bml3mk5/USBKeyboard4S1/Software/USBKeyboard4S1.X/interrupt.h

/** @file   interrupt.h
 *
 *  @author Sasaji
 *  @date   2018/02/10
 *
 * 	@brief  interrupt 
 */

#ifndef INTERRUPT_H
#define	INTERRUPT_H

#ifdef	__cplusplus
extern "C" {
#endif

void INTR_Init(void);


#ifdef	__cplusplus
}
#endif

#endif	/* INTERRUPT_H */
