bml3mk5/USBKeyboard4S1/Software/USBKeyboard4S1.X/timer_2.h

/** @file   timer_2.h
 *
 *  @author Sasaji
 *  @date   2018/02/10
 *
 * 	@brief  interrupt 
 */

#ifndef TIMER_2_H
#define	TIMER_2_H

#ifdef	__cplusplus
extern "C" {
#endif

//void Timer2_Init(void);


#ifdef	__cplusplus
}
#endif

#endif	/* TIMER_2_H */
